Tbthanh/Logic_Design_time_display_with_day/Document/graphics_files/time_display_with_day_PCB_des.PDF

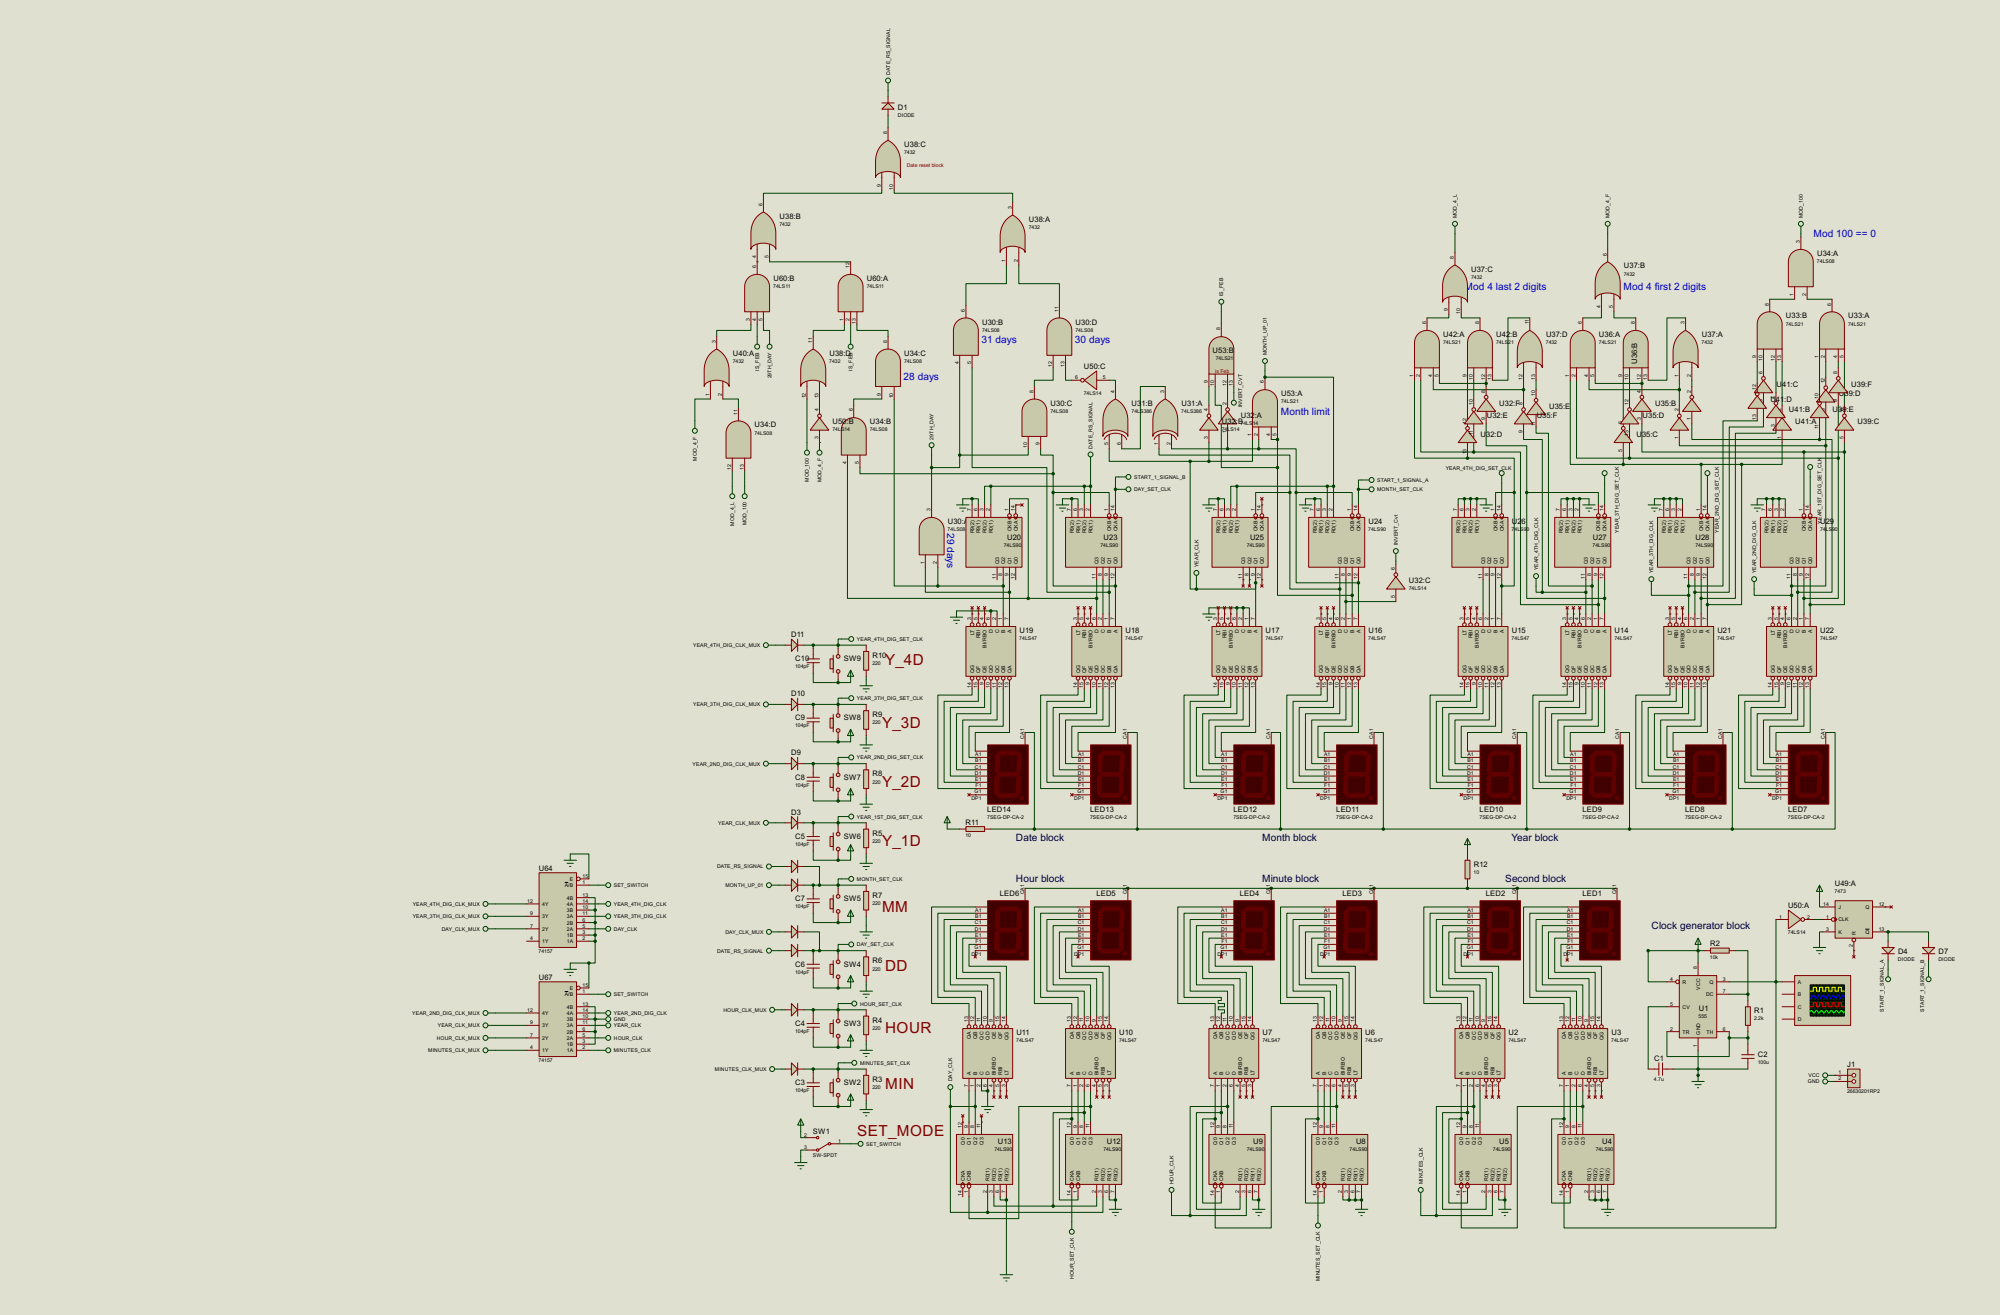
[picture p8: page 1]

LED5 | LED4 | LED3 | LED2 | LED1
