Tbthanh/Logic_Design_time_display_with_day/Document/graphics_files/Nearly_synchronous_using_74192.PDF

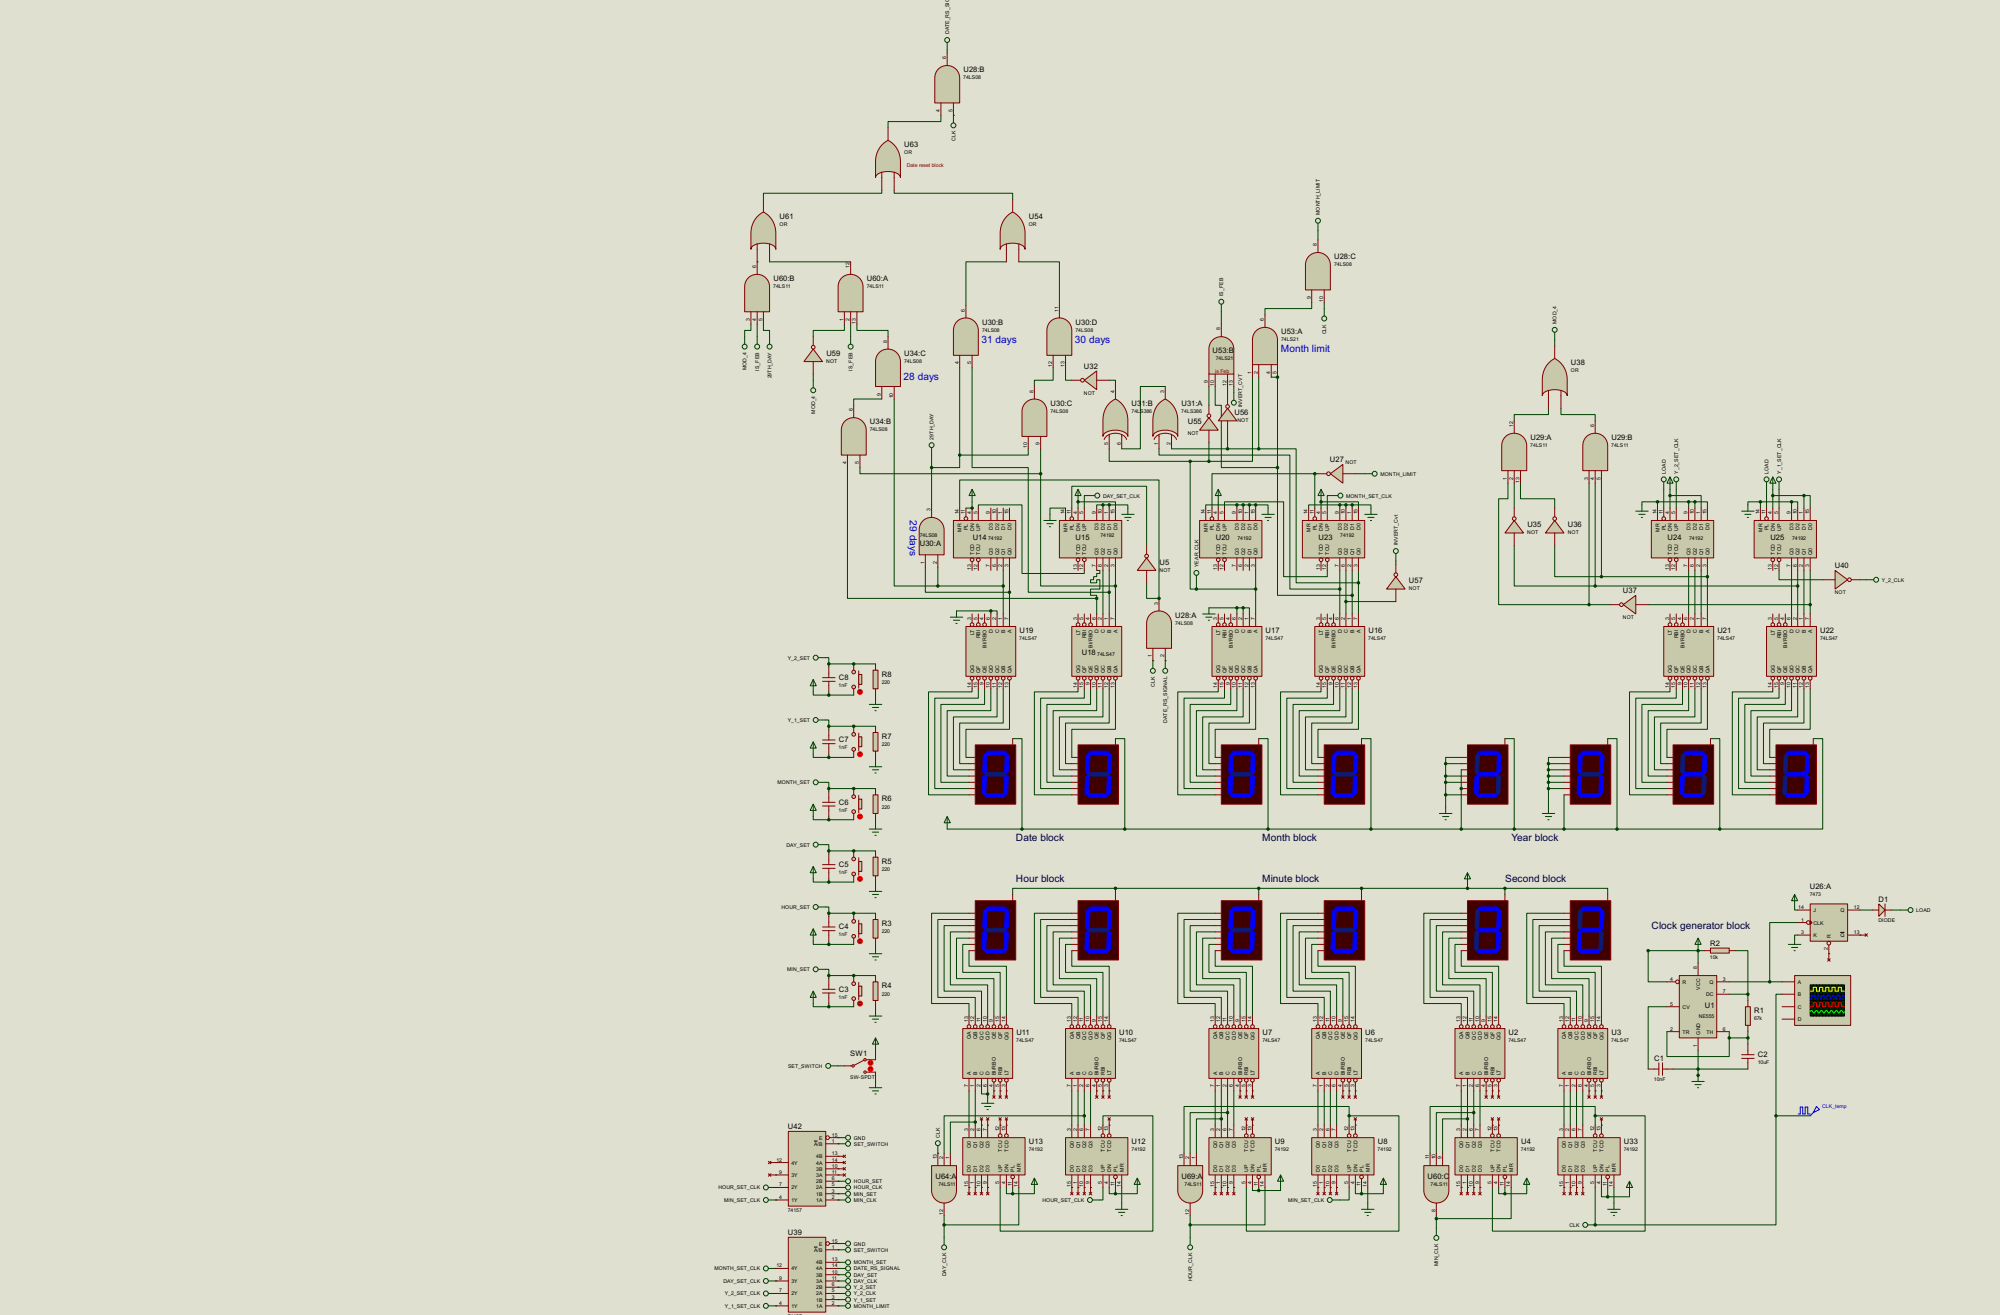
[picture p10: page 1]
