Tbthanh/Logic_Design_time_display_with_day/Document/graphics_files/OLD_time_display_with_day_PCB_des_old_version (4).PDF

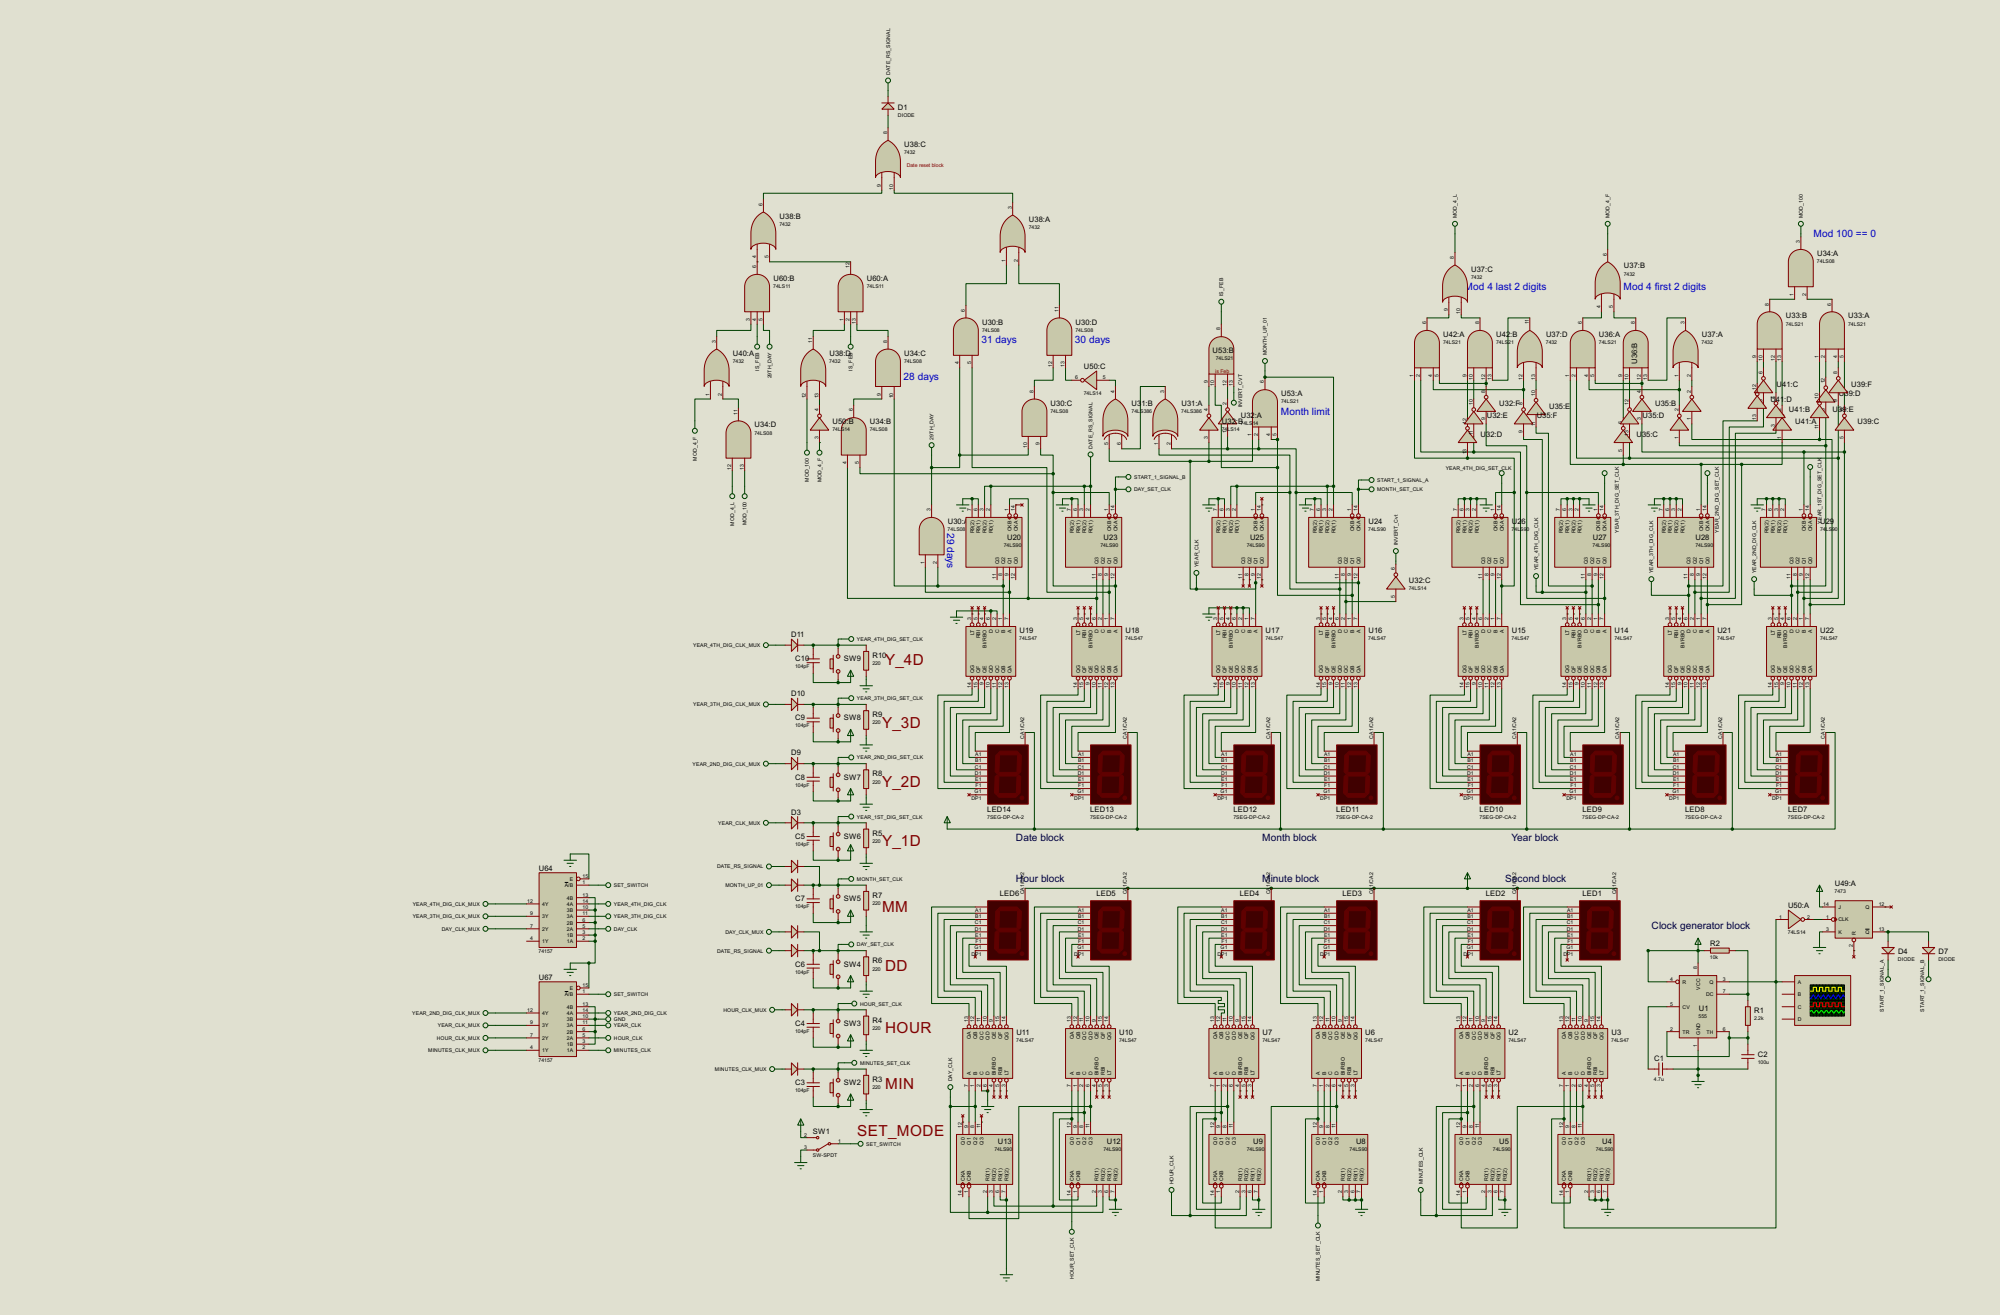
[picture p11: page 1]

LED5 | LED4 | LED3 | LED2 | LED1
